HierzBettina/ble-dev-kit/firmware/Blinky/Source/HM-10.h

#ifndef HM_10
#define HM_10

#define PIN0 P1_3
#define PIN1 P1_2
#define PIN2 P1_1
#define PIN3 P1_0

#define PIN4 P0_7
#define PIN5 P0_6
#define PIN6 P0_5
#define PIN7 P0_4
#define PIN8 P0_3
#define PIN9 P0_2
#define PIN10 P0_1
#define PIN11 P0_0

#endif /* HM-10 */
